SebastienTr/Marvin/docs/concepts/concept_A_fanou.png

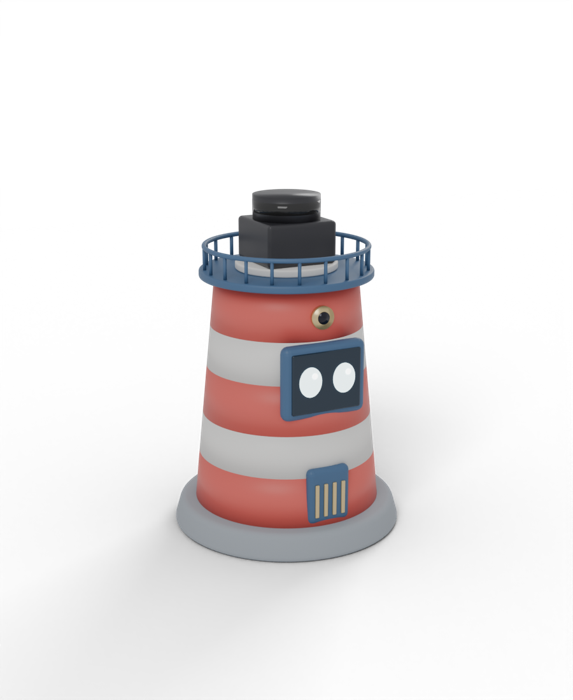
docs/concepts/concept_A_fanou.png
