SebastienTr/Marvin/docs/concepts/concept_B_hulotte.png

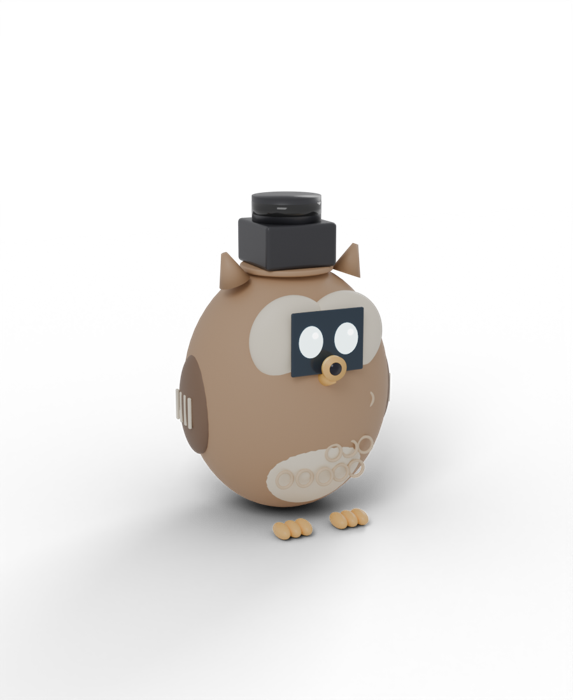
docs/concepts/concept_B_hulotte.png
