SebastienTr/Marvin/docs/concepts/concepts_board_v2.jpg

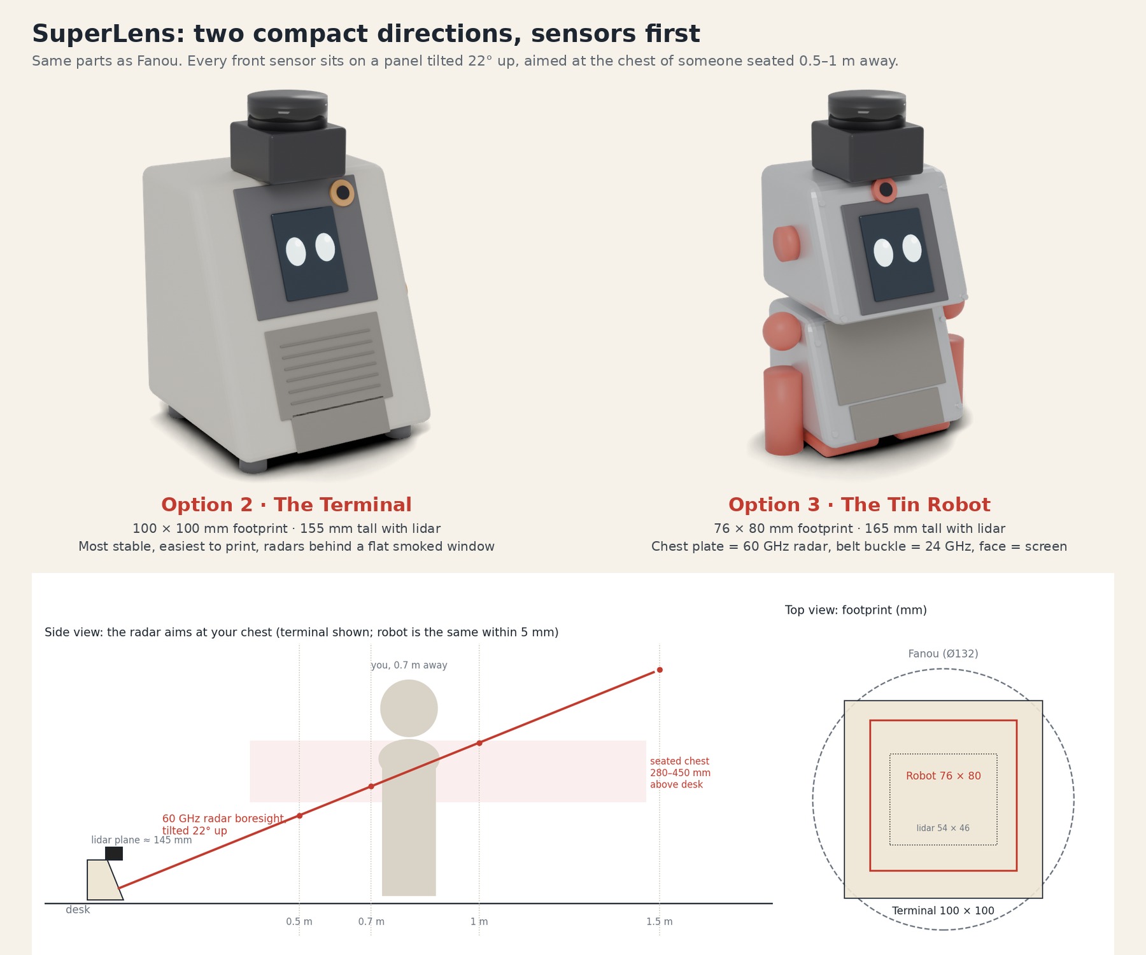
docs/concepts/concepts_board_v2.jpg
