SebastienTr/Marvin/docs/concepts/sightlines.png

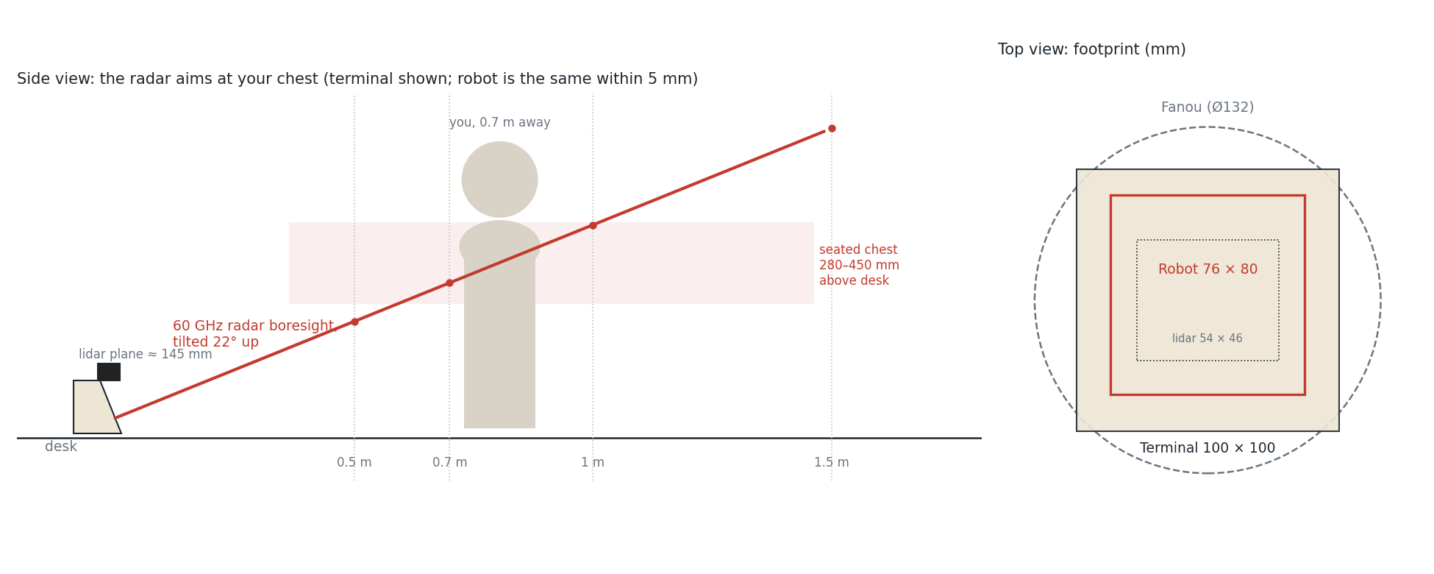
docs/concepts/sightlines.png
