SebastienTr/Marvin/docs/images/face_demo.gif

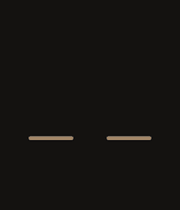
docs/images/face_demo.gif
