SebastienTr/Marvin/docs/images/fanou_back.png

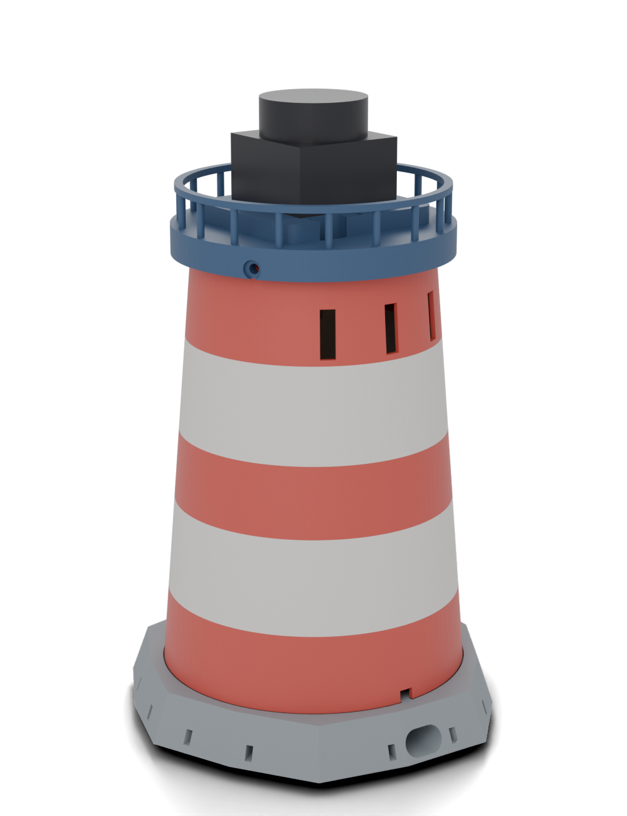
docs/images/fanou_back.png
