SebastienTr/Marvin/docs/images/fanou_exploded.png

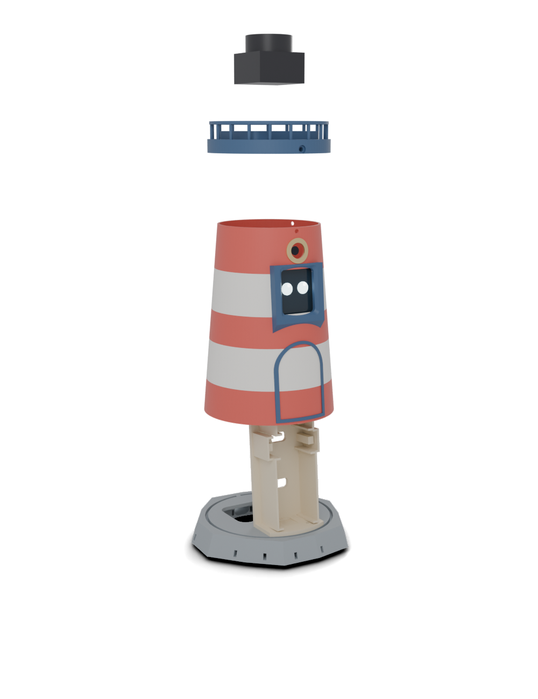
docs/images/fanou_exploded.png
