SebastienTr/Marvin/docs/images/fanou_face.png

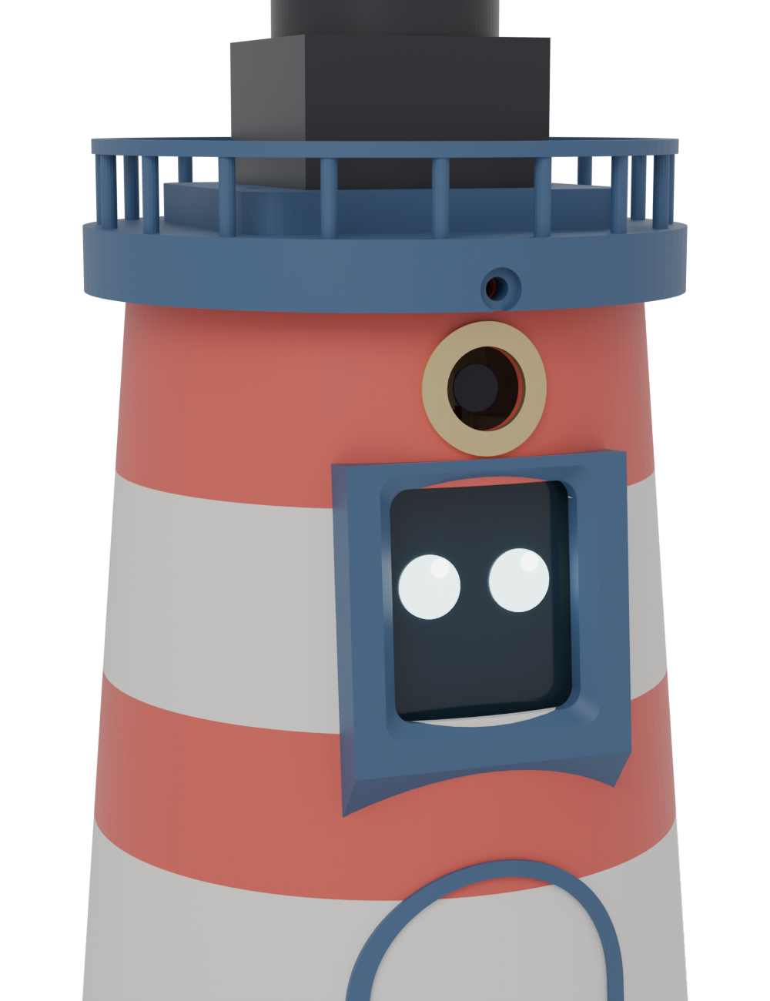
docs/images/fanou_face.png
