SebastienTr/Marvin/docs/images/fanou_front.png

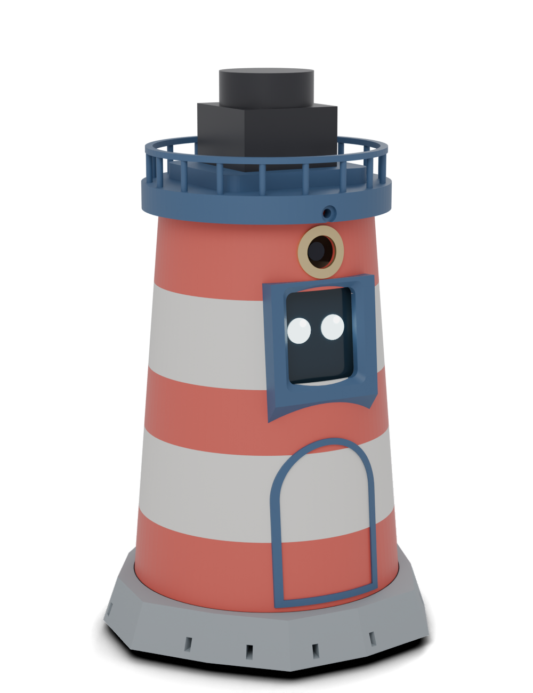
docs/images/fanou_front.png
