SebastienTr/Marvin/docs/images/robot_side.png

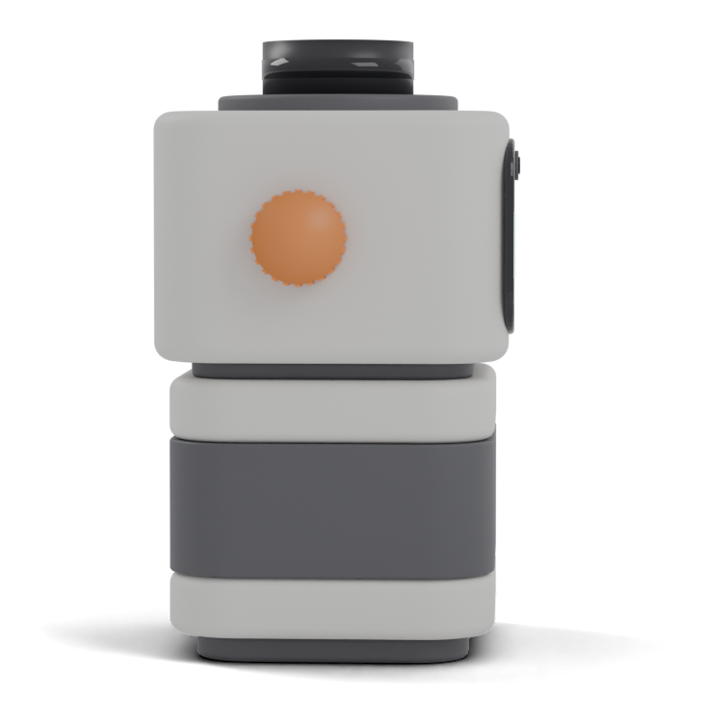
docs/images/robot_side.png
