SebastienTr/Marvin/host-java/marvin-contracts/golden/face/attentive.png

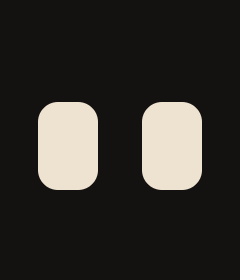
host-java/marvin-contracts/golden/face/attentive.png
