SebastienTr/Marvin/host-java/marvin-contracts/golden/face/calm.png

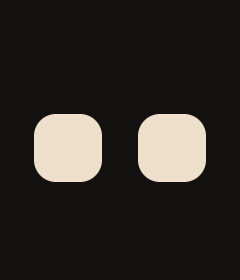
host-java/marvin-contracts/golden/face/calm.png
