SebastienTr/Marvin/host-java/marvin-contracts/golden/face/content.png

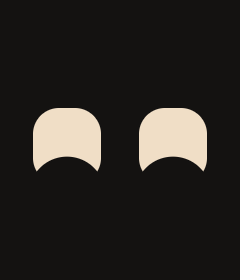
host-java/marvin-contracts/golden/face/content.png
