SebastienTr/Marvin/host-java/marvin-contracts/golden/face/sleepy.png

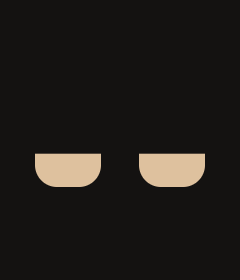
host-java/marvin-contracts/golden/face/sleepy.png
